aleor99/pedometer_project/GUI FINALE/4.png

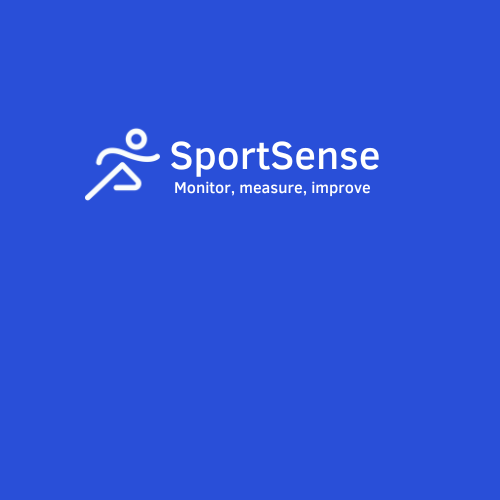
GUI FINALE/4.png
