aleor99/pedometer_project/PSOC/Codice_PSoC.cydsn/codegentemp/Pin_BUTTON_aliases.h

/*******************************************************************************
* File Name: Pin_BUTTON.h  
* Version 2.20
*
* Description:
*  This file contains the Alias definitions for Per-Pin APIs in cypins.h. 
*  Information on using these APIs can be found in the System Reference Guide.
*
* Note:
*
********************************************************************************
* Copyright 2008-2015, Cypress Semiconductor Corporation.  All rights reserved.
* You may use this file only in accordance with the license, terms, conditions, 
* disclaimers, and limitations in the end user license agreement accompanying 
* the software package with which this file was provided.
*******************************************************************************/

#if !defined(CY_PINS_Pin_BUTTON_ALIASES_H) /* Pins Pin_BUTTON_ALIASES_H */
#define CY_PINS_Pin_BUTTON_ALIASES_H

#include "cytypes.h"
#include "cyfitter.h"


/***************************************
*              Constants        
***************************************/
#define Pin_BUTTON_0			(Pin_BUTTON__0__PC)
#define Pin_BUTTON_0_INTR	((uint16)((uint16)0x0001u << Pin_BUTTON__0__SHIFT))

#define Pin_BUTTON_INTR_ALL	 ((uint16)(Pin_BUTTON_0_INTR))

#endif /* End Pins Pin_BUTTON_ALIASES_H */


/* [] END OF FILE */
