aleor99/pedometer_project/PSOC/Codice_PSoC.cydsn/codegentemp/isr_Timer.h

/*******************************************************************************
* File Name: isr_Timer.h
* Version 1.71
*
*  Description:
*   Provides the function definitions for the Interrupt Controller.
*
*
********************************************************************************
* Copyright 2008-2015, Cypress Semiconductor Corporation.  All rights reserved.
* You may use this file only in accordance with the license, terms, conditions, 
* disclaimers, and limitations in the end user license agreement accompanying 
* the software package with which this file was provided.
*******************************************************************************/
#if !defined(CY_ISR_isr_Timer_H)
#define CY_ISR_isr_Timer_H


#include <cytypes.h>
#include <cyfitter.h>

/* Interrupt Controller API. */
void isr_Timer_Start(void);
void isr_Timer_StartEx(cyisraddress address);
void isr_Timer_Stop(void);

CY_ISR_PROTO(isr_Timer_Interrupt);

void isr_Timer_SetVector(cyisraddress address);
cyisraddress isr_Timer_GetVector(void);

void isr_Timer_SetPriority(uint8 priority);
uint8 isr_Timer_GetPriority(void);

void isr_Timer_Enable(void);
uint8 isr_Timer_GetState(void);
void isr_Timer_Disable(void);

void isr_Timer_SetPending(void);
void isr_Timer_ClearPending(void);


/* Interrupt Controller Constants */

/* Address of the INTC.VECT[x] register that contains the Address of the isr_Timer ISR. */
#define isr_Timer_INTC_VECTOR            ((reg32 *) isr_Timer__INTC_VECT)

/* Address of the isr_Timer ISR priority. */
#define isr_Timer_INTC_PRIOR             ((reg8 *) isr_Timer__INTC_PRIOR_REG)

/* Priority of the isr_Timer interrupt. */
#define isr_Timer_INTC_PRIOR_NUMBER      isr_Timer__INTC_PRIOR_NUM

/* Address of the INTC.SET_EN[x] byte to bit enable isr_Timer interrupt. */
#define isr_Timer_INTC_SET_EN            ((reg32 *) isr_Timer__INTC_SET_EN_REG)

/* Address of the INTC.CLR_EN[x] register to bit clear the isr_Timer interrupt. */
#define isr_Timer_INTC_CLR_EN            ((reg32 *) isr_Timer__INTC_CLR_EN_REG)

/* Address of the INTC.SET_PD[x] register to set the isr_Timer interrupt state to pending. */
#define isr_Timer_INTC_SET_PD            ((reg32 *) isr_Timer__INTC_SET_PD_REG)

/* Address of the INTC.CLR_PD[x] register to clear the isr_Timer interrupt. */
#define isr_Timer_INTC_CLR_PD            ((reg32 *) isr_Timer__INTC_CLR_PD_REG)


#endif /* CY_ISR_isr_Timer_H */


/* [] END OF FILE */
